PaulWozny/NoiseTester/pcb/calc/imgs/20181007-200341.png

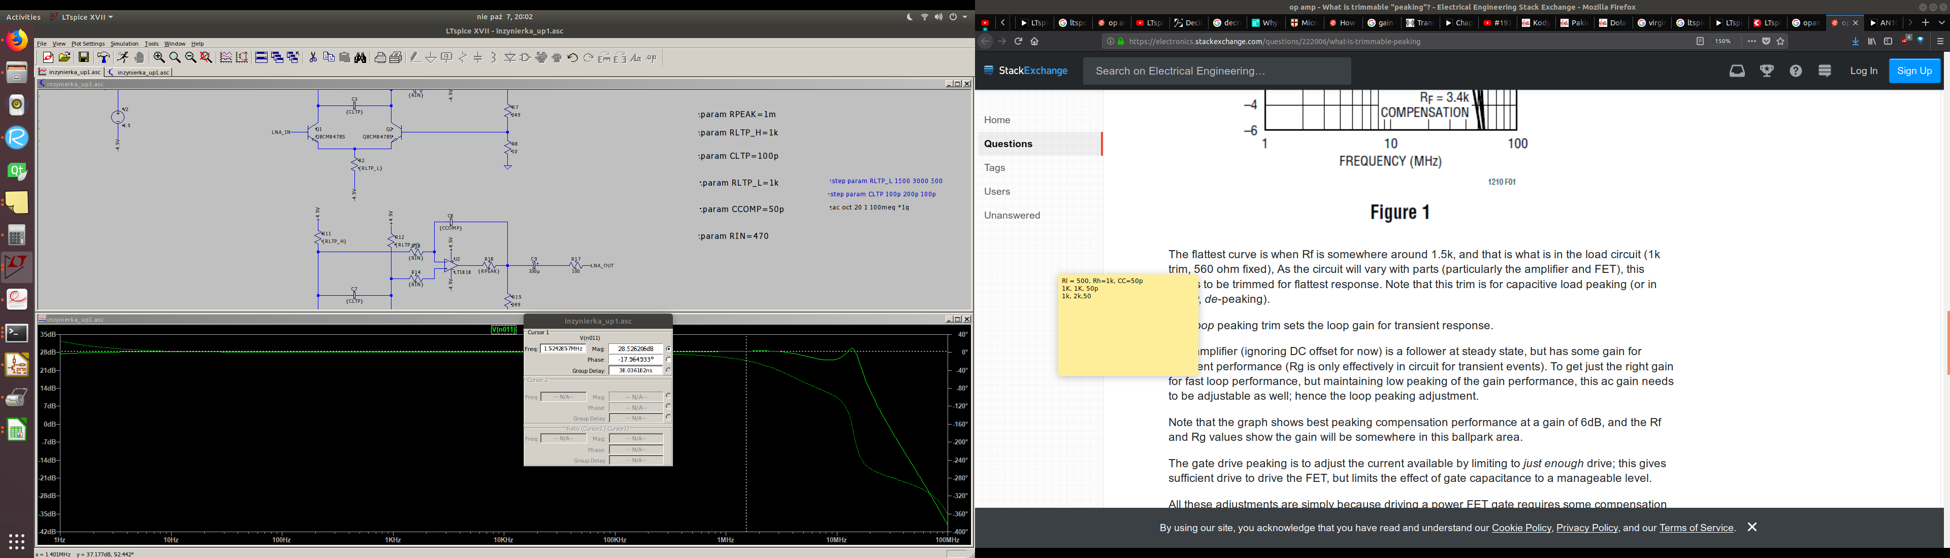
pcb/calc/imgs/20181007-200341.png
