PaulWozny/NoiseTester/pcb/spice/inzynierka.asc

C1: cap; 120p
C2: cap; 330µ; V=16 Irms=0.578 Rser=0.4 Lser=2n Rpar=500k
C3: cap; {CLTP}; V=50 Irms=0 Rser=0 Lser=0 mfg="Murata" pn="GCM1555C1H331JA16" type="C0G"
C4: cap; 330µ; V=16 Irms=0.578 Rser=0.4 Lser=2n Rpar=500k
C5: cap; 120p; V=50 Irms=0 Rser=0 Lser=0 mfg="Murata" pn="GRM0335C1H121JA01" type="C0G"
C6: polcap; 330µ; V=16 Irms=2.22261 Rser=0.05 Lser=0 mfg="KEMET" pn="T521X337M016ATE050" type="Tantalum"
C7: cap; {CLTP}; V=50 Irms=0 Rser=0 Lser=0
C8: cap; 22p; V=50 Irms=0 Rser=0 Lser=0
C9: cap; 330µ; V=16 Irms=0.578 Rser=0.4 Lser=2n Rpar=500k
C10: cap; {CLTP}; V=50 Irms=0 Rser=0 Lser=0 mfg="Murata" pn="GCM1555C1H331JA16" type="C0G"
C11: cap; 120p; V=50 Irms=0 Rser=0 Lser=0 mfg="Murata" pn="GRM0335C1H121JA01" type="C0G"
C12: cap; 330µ; V=16 Irms=0.578 Rser=0.4 Lser=2n Rpar=500k
C13: cap; {CLTP}; V=50 Irms=0 Rser=0 Lser=0 mfg="Murata" pn="GCM1555C1H331JA16" type="C0G"
C14: cap; 120p; V=50 Irms=0 Rser=0 Lser=0 mfg="Murata" pn="GRM0335C1H121JA01" type="C0G"
C15: cap; 330µ; V=16 Irms=0.578 Rser=0.4 Lser=2n Rpar=500k
C16: cap; 4.7µ; V=16 Irms=0 Rser=0 Lser=0 mfg="Murata" pn="GCM31CR71C475MA37" type="X7R"
C17: cap; 4.7µ; V=16 Irms=0 Rser=0 Lser=0 mfg="Murata" pn="GCM31CR71C475MA37" type="X7R"
C18: cap; 330µ; V=16 Irms=0.578 Rser=0.4 Lser=2n Rpar=500k
C19: cap; 330µ; V=16 Irms=0.578 Rser=0.4 Lser=2n Rpar=500k
C20: cap; 100p
C21: cap; 150p
C22: cap; 22p
C23: cap; 330µ; V=16 Irms=0.578 Rser=0.4 Lser=2n Rpar=500k
C24: cap; 330µ; V=16 Irms=0.578 Rser=0.4 Lser=2n Rpar=500k
C25: cap; 1200p
C26: cap; 1000p
C27: cap; 1500p
C28: cap; 220p
C29: cap; 330µ; V=16 Irms=0.578 Rser=0.4 Lser=2n Rpar=500k
C30: cap; 330µ; V=16 Irms=0.578 Rser=0.4 Lser=2n Rpar=500k
Q1: npn; QBCM847BS
Q2: npn; QBCM847BS
Q3: npn; QBCM847BS
Q4: npn; QBCM847BS
Q5: npn; QBCM847BS
Q6: npn; QBCM847BS
Q7: npn; QBCM847BS
Q8: npn; QBCM847BS
R1: res; 499; tol=1 pwr=0.1
R2: res; {RLTP_L}; tol=1 pwr=0.1
R3: res; {RLTP_H}; tol=1 pwr=0.1
R4: res; {RLTP_H}; tol=1 pwr=0.1
R5: res; 470; tol=1 pwr=0.1
R6: res; 470; tol=1 pwr=0.1
R7: res; 249; tol=1 pwr=0.1
R8: res; 10; tol=1 pwr=0.1
R9: res; 100; tol=1 pwr=0.1
R10: res; {RLTP_L}; tol=1 pwr=0.1
R11: res; {RLTP_H}; tol=1 pwr=0.1
R12: res; {RLTP_H}; tol=1 pwr=0.1
R13: res; 220; tol=1 pwr=0.1
R14: res; 220; tol=1 pwr=0.1
R15: res; 249; tol=1 pwr=0.1
R16: res; 10; tol=1 pwr=0.1
R17: res; 100; tol=1 pwr=0.1
R18: res; {RLTP_L}; tol=1 pwr=0.1
R19: res; {RLTP_H}; tol=1 pwr=0.1
R20: res; {RLTP_H}; tol=1 pwr=0.1
R21: res; 470; tol=1 pwr=0.1
R22: res; 470; tol=1 pwr=0.1
R23: res; 249; tol=1 pwr=0.1
R24: res; 10; tol=1 pwr=0.1
R25: res; 100; tol=1 pwr=0.1
R26: res; {RLTP_L}; tol=1 pwr=0.1
R27: res; {RLTP_H}; tol=1 pwr=0.1
R28: res; {RLTP_H}; tol=1 pwr=0.1
R29: res; 470; tol=1 pwr=0.1
R30: res; 470; tol=1 pwr=0.1
R31: res; 249; tol=1 pwr=0.1
R32: res; 10; tol=1 pwr=0.1
R33: res; 100; tol=1 pwr=0.1
R34: res; 500; tol=1 pwr=0.1
R35: res; 2k
R36: res; 5k76
R37: res; 100; tol=1 pwr=0.1
R38: res; 2k
R39: res; 49.9; tol=1 pwr=0.1
R40: res; 1k69
R41: res; 1k24
R42: res; 4k02
R43: res; 2k15
R44: res; 49.9; tol=1 pwr=0.1
R45: res; 1k69
R46: res; 1k24
R47: res; 4k02
R48: res; 2k15
R49: res; 49.9; tol=1 pwr=0.1
U1: LT1818
U2: LT1818
U3: LT1818
U4: LT1818
U5: LT6232
U6: LT6232
U7: LT6232
U8: LT1364
U9: LT6232
U10: LT1364
U11: LT6232
U12: LT1364
V2: voltage; 4.5
V3: voltage; 4.5
VIN: voltage; SINE(10 1u 200 1u); AC 1u
Named nets: 0, +4.5V, -4.5V, LNA_OUT, LNA_IN
.ac oct 20 1 1g
********************************************
* BCM847BS
* NXP Semiconductors
* Matched double NPN/NPN transistor
* IC   = 100 mA
* VCEO = 45 V 
* hFE  = 200 - 450 @ 5V/2mA
* Package pinning does not match Spice model pinning.
* Package: SOT 363
* Package Pin 1;4: Emitter      TR1;TR2
* Package Pin 2;5: Base         TR1;TR2
* Package Pin 3;6: Collector    TR2;TR1
* Extraction date (week/year): 14/2006
* Simulator: Spice 2        
********************************************
* Please note: The following model is to be used twice in 
* schematic due to equality of both transistors.
*
.MODEL QBCM847BS NPN
+     IS = 1.822E-14 
+     NF = 0.9932 
+     ISE= 2.894E-16 
+     NE = 1.4 
+     BF = 324.4 
+     IKF = 0.109 
+     VAF = 82 
+     NR = 0.9931 
+     ISC = 9.982E-12 
+     NC = 1.763 
+     BR = 8.29 
+     IKR = 0.09 
+     VAR = 17.9 
+     RB = 10 
+     IRB = 5E-06 
+     RBM = 5 
+     RE = 0.649 
+     RC = 0.7014 
+     CJE = 1.244E-11 
+     VJE = 0.7579 
+     MJE = 0.3656 
+     TF = 4.908E-10 
+     XTF = 9.51 
+     VTF = 2.927 
+     ITF = 0.3131 
+     PTF = 0 
+     CJC = 3.347E-12 
+     VJC = 0.5463 
+     MJC = 0.391 
+     XCJC = 0.6193 
+     TR = 9E-08 
+     CJS = 0 
+     VJS = 0.75 
+     MJS = 0.333 
+     XTB = 0 
+     XTI = 3 
+     EG = 1.11 
+     FC = 0.979
.param RLTP_H=2k2
.param RLTP_L=1k
.param CLTP=100p
.step param RLTP_L 1500 3000 500
.step param CLTP 100p 200p 100p
330uF - tantalum capacitor  TAJE337M016RNJ
